HenriquesLab/NanoJ-Fluidics/Files/3D Printing Parts/MMeyer_Pumpy_1_1beta.stl

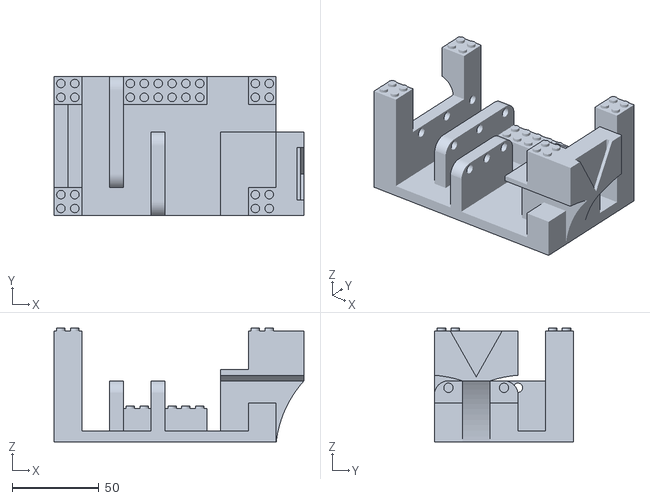
[picture p18: CAD file, 2018-08-28]
Files/3D Printing Parts/MMeyer_Pumpy_1_1beta.stl
144.0 x 80.0 x 65.6
