HenriquesLab/NanoJ-Fluidics/Files/3D Printing Parts/MMeyer_VSlotLegoAdaptor_1_1beta.stl

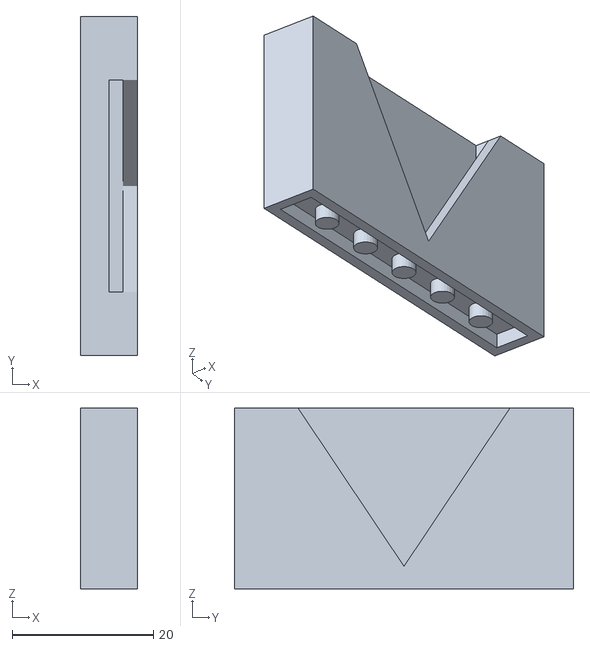
[picture p19: CAD file, 2018-08-28]
Files/3D Printing Parts/MMeyer_VSlotLegoAdaptor_1_1beta.stl
8.00 x 48.0 x 25.6
