HenriquesLab/NanoJ-Fluidics/Files/3D Printing Parts/MMeyer_ReplacementForLegoPartsMinosLinearActuator_1_1beta.stl

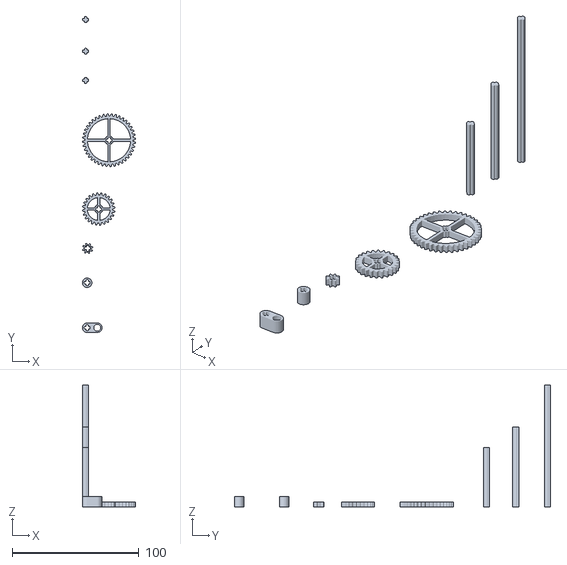
[picture p20: CAD file, 2018-08-28]
Files/3D Printing Parts/MMeyer_ReplacementForLegoPartsMinosLinearActuator_1_1beta.stl
42.0 x 249.3 x 96.0
