HenriquesLab/NanoJ-Fluidics/Files/3D Printing Parts/LSaunders_ActuatorClamp_1_0.stl

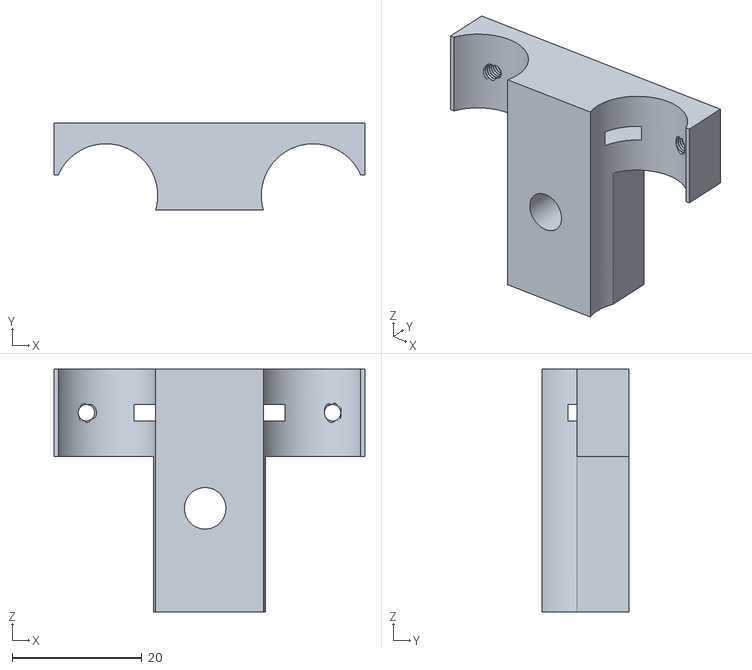
[picture p21: CAD file, 2018-08-28]
Files/3D Printing Parts/LSaunders_ActuatorClamp_1_0.stl
48.0 x 13.4 x 37.5
