HenriquesLab/NanoJ-Fluidics/Files/3D Printing Parts/LSaunders_SyringeClamp_1_0.stl

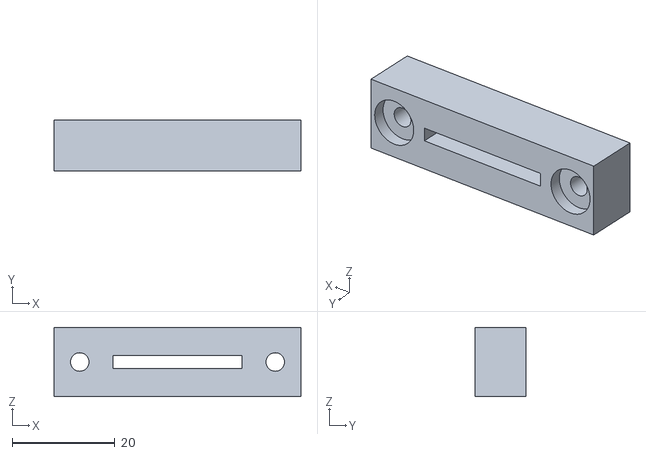
[picture p22: CAD file, 2018-08-28]
Files/3D Printing Parts/LSaunders_SyringeClamp_1_0.stl
48.0 x 10.0 x 13.5
