HenriquesLab/NanoJ-Fluidics/Files/3D Printing Parts/LSaunders_Platform_1_0.stl

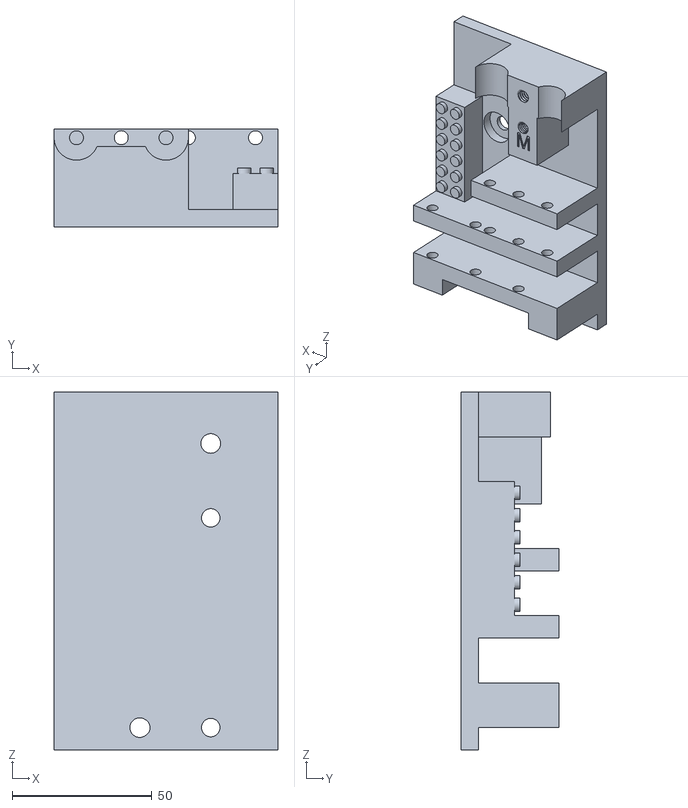
[picture p23: CAD file, 2018-08-28]
Files/3D Printing Parts/LSaunders_Platform_1_0.stl
80.0 x 35.2 x 128.0
