HenriquesLab/NanoJ-Fluidics/Files/3D Printing Parts/MMeyer_Pumpy_1_0.stl

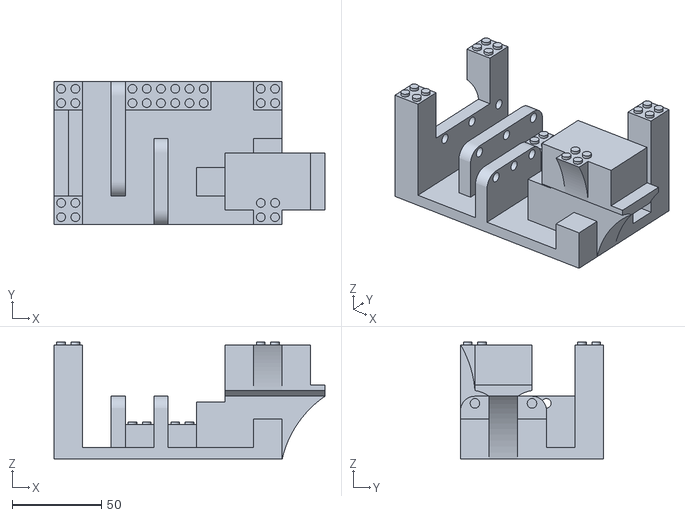
[picture p24: CAD file, 2018-08-24]
Files/3D Printing Parts/MMeyer_Pumpy_1_0.stl
152.0 x 80.0 x 65.6
